the-butcher/letter_rings/letter_rings_arduino/src/Chars.h

#ifndef Chars_h
#define Chars_h

#include <Arduino.h>

#include "Define.h"

class Chars {
private:
public:

    static char__________t chars[CHARS______________NUM];

    static void step();

    static bool powerup();

};

#endif
